jp112sdl/328RFStamp/blender/331.png

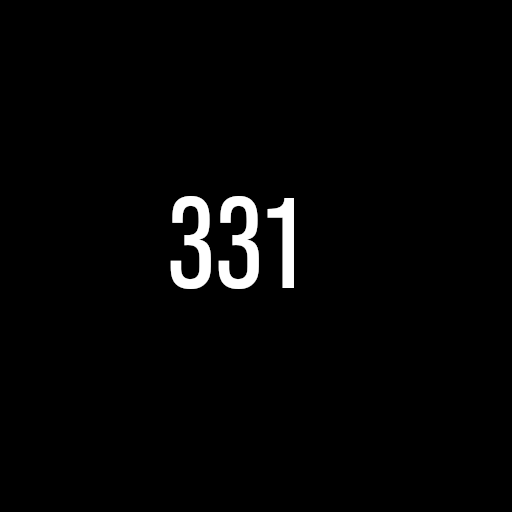
blender/331.png
